partlyhuman/wqv-blink/firmware/wqv310/src/app.cpp

#include "app.h"

#include <algorithm>
#include <cstring>

#include "log.h"

namespace App {

const char* TAG = "App";

constexpr char RESPONSE_BDY0[] = "BDY0";
constexpr uint8_t RINF_EXTRA_DATA[]{0x00, 0x00, 0x10, 0xFF, 0xFF, 0x11, 0xFF, 0xFF};
constexpr uint8_t RCMD_EXTRA_DATA[]{0x00, 0x00, 0x20, 0x00, 0x01, 0x00, 0x01};
constexpr uint8_t RIMG_EXTRA_DATA[]{0x00, 0x00, 0x00, 0x01, 0x01, 0x01, 0x08, 0x00, 0x06, 0x00, 0x02, 0x07, 0x08,
                                    0x00, 0x06, 0x00, 0x06, 0x40, 0x04, 0xB0, 0x05, 0x00, 0x03, 0xC0, 0x04, 0x00,
                                    0x03, 0x00, 0x03, 0x20, 0x02, 0x58, 0x02, 0x80, 0x01, 0xE0, 0x01, 0x40, 0x00,
                                    0xF0, 0x03, 0xC4, 0x20, 0x04, 0x01, 0xC4, 0x20, 0x05, 0x00, 0x00, 0x18, 0x00};

std::span<const uint8_t> fill(std::span<const uint8_t> cmd, uint8_t session) {
    static std::vector<uint8_t> CMD_BUFFER(64);
    std::replace_copy(cmd.begin(), cmd.end(), CMD_BUFFER.begin(), SESH, session);
    return std::span(CMD_BUFFER).subspan(0, cmd.size());
}

// NOTE this expects the full frame, as a convenience it also acts on the session header
// even though that's not part of the application layer
std::vector<uint8_t> makeResponse(Frame::Frame frame) {
    const size_t CMD_SIZE = 44;
    if (frame.data.size() < CMD_SIZE) {
        LOGE(TAG, "Size too small to be app command packet");
        return {};
    }

    std::string cmd = getCmdName(frame);
    std::span<const uint8_t> extraData;
    int8_t shifts;
    if (cmd == "RINF") {
        extraData = RINF_EXTRA_DATA;
        shifts = -0x0C;
    } else if (cmd == "RCMD") {
        extraData = RCMD_EXTRA_DATA;
        shifts = -0x0D;
    } else if (cmd == "RIMG") {
        extraData = RIMG_EXTRA_DATA;
        shifts = 0x20;
    }
    std::vector<uint8_t> response(frame.data.begin(), frame.data.begin() + CMD_SIZE);
    response.reserve(response.size() + sizeof(uint32_t) + extraData.size());
    auto src = frame.data;

    // 1. First bytes: swap [session] 03 -> 03 [session]
    response[0] = src[1];
    response[1] = src[0];

    // 2. Last byte 0x2b: 02 -> 01
    response[0x2b] = 0x01;

    // 3. Byte 0xf: 00 -> 40
    response[0xf] = 0x40;

    // 4. Byte 0x18 & 0x20: swap
    response[0x18] = src[0x20];
    response[0x20] = src[0x18];

    // 5. Byte 0x29 unchanged

    // 6. Shifted fields
    response[0x9] = static_cast<uint8_t>(static_cast<int8_t>(src[0x9]) + shifts);
    response[0xd] = static_cast<uint8_t>(static_cast<int8_t>(src[0xd]) + shifts);
    response[0x13] = static_cast<uint8_t>(static_cast<int8_t>(src[0x13]) + shifts);

    // Append "BDY0" without \0
    response.insert(response.end(), std::begin(RESPONSE_BDY0), std::end(RESPONSE_BDY0) - 1);

    // Append 4-byte size of extended data
    uint32_t extraSize = static_cast<uint32_t>(extraData.size());
    response.push_back(static_cast<uint8_t>((extraSize >> 24) & 0xFF));
    response.push_back(static_cast<uint8_t>((extraSize >> 16) & 0xFF));
    response.push_back(static_cast<uint8_t>((extraSize >> 8) & 0xFF));
    response.push_back(static_cast<uint8_t>(extraSize & 0xFF));

    // Append extended data
    response.insert(response.end(), extraData.begin(), extraData.end());
    return response;
}

std::pair<std::string, std::vector<uint8_t>> makeFilRplResponse(Frame::Frame frame) {
    constexpr uint8_t RPL0_CMD[]{0,    0,    0x00, 0x00, 0x00, 0x20, 0x03, 0xFF, 0x00, 0x38, 0x10, 0xC1, 0x00, 0x34,
                                 0x58, 0x40, 0x00, 0x00, 0x00, 0x2E, 0x08, 0x00, 0x74, 0x03, 0x00, 0x00, 0x00, 0x00,
                                 0x08, 0x00, 0x74, 0x03, 0x10, 0x00, 0x00, 0x00, 0x00, 0x08, 0x00, 0x08, 0x00, 0,
                                 0x00, 0x01, 0x52, 0x50, 0x4C, 0x30, 0x00, 0x00, 0x00, 0x0E, 0x01, 0x00, 0x00, 0x00,
                                 0x00, 0x00, 0x00, 0x00, 0x00, 0x00, 0x00, 0x00, 0x00, 0x00};

    auto src = frame.data;
    std::vector<uint8_t> response(std::begin(RPL0_CMD), std::end(RPL0_CMD));
    response[0] = src[1];
    response[1] = src[0];
    response[0x29] = src[0x31];
    auto fileNameSpan = src.subspan(0x4C, 12);
    std::memcpy(response.data() + 0x36, fileNameSpan.data(), fileNameSpan.size());
    std::string fileName(reinterpret_cast<const char *>(fileNameSpan.data()), fileNameSpan.size());
    return {fileName, response};
}

std::string getCmdName(Frame::Frame frame) {
    return Frame::extractString(frame, frame.data.size() - 4, 4);
}

std::span<const uint8_t> getAppPayload(Frame::Frame frame) {
    if (frame.error || frame.data.size() < std::size(CLIENT_APP_PACKET)) {
        return {};
    }
    // Could reject if doesn't start with session header
    return frame.data.subspan(std::size(CLIENT_APP_PACKET));
}

}  // namespace App
