partlyhuman/wqv-blink/firmware/wqv310/src/meta.cpp

#include "meta.h"

#include <FFat.h>
#include <PSRamFS.h>

#include <cstring>
#include <ctime>

#include "log.h"
namespace Meta {

const static char *TAG = "Meta";

time_t timestampToTime(const Timestamp src) {
    tm t{};
    t.tm_year = (2000 + src.year2k) - 1900;
    t.tm_mon = src.month - 1;
    t.tm_mday = src.day;
    t.tm_hour = src.hour;
    t.tm_min = src.minute;
    t.tm_isdst = 0;
    time_t time = mktime(&t);
    return time;
}

void setSystemTime(const time_t time) {
    timeval epoch = {time, 0};
    settimeofday((const timeval *)&epoch, 0);
}

std::string trimTrailingSpaces(std::string src) {
    if (src.find_first_not_of(' ') == std::string::npos) return "";
    return src.substr(0, src.find_last_not_of(' ') + 1);
}

std::pair<std::string, Timestamp> getMetaFromJpegMarker(fs::File src) {
    try {
        // Let's make things easy on ourselves and assume the marker is in the first 512 bytes of the file
        char headerBuffer[512];
        if (!src) throw std::runtime_error("Couldn't find file");
        src.seek(0);
        size_t bytesRead = src.readBytes(headerBuffer, sizeof(headerBuffer));
        src.seek(0);

        std::span header(headerBuffer, headerBuffer + bytesRead);
        auto iter = header.begin();

        if (iter[0] != 0xff || iter[1] != 0xd8) throw std::runtime_error("Invalid SOI");
        iter += 2;

        // Make sure we at least have enough to read the marker
        while ((iter + 4) < header.end()) {
            if (iter[0] != 0xff) throw std::runtime_error("Expected 0xff in marker");
            uint8_t marker = iter[1];
            iter += 2;

            // len includes the bytes themselves, but we don't want to consume them
            uint16_t len = (iter[0] << 8) | iter[1];
            LOGV(TAG, "Encountered marker %02x of length %d", marker, len);
            if (marker != 0xe2) {
                iter += len;
                continue;
            }

            LOGD(TAG, "Found APP2 marker, extracting metadata");
            // consume the length too, we want to point to the data
            const char *payload = header.data() + (iter - header.begin()) + 2;
            size_t payloadLen = len - 2;

            if (payloadLen < sizeof(Timestamp)) throw std::runtime_error("APP2 marker not big enough for timestamp");

            size_t strLen = payloadLen - sizeof(Timestamp);
            Timestamp timestamp;
            std::memcpy(&timestamp, payload + strLen, sizeof(Timestamp));

            std::string title;
            bool isAscii = std::all_of(payload, payload + strLen, [](char b) { return b <= 0x7F; });
            if (isAscii) {
                title = trimTrailingSpaces(std::string(payload, strLen));
            }
            return std::pair(title, timestamp);
        }

        LOGE(TAG, "Couldn't find APP2 marker in JPEG, no metadata");

    } catch (std::exception &e) {
        LOGE(TAG, "%s", e.what());
    }
    return {};
}

bool copyRename(fs::File src, std::string destPath, size_t size) {
    auto startTime = millis();

    File dst = FFat.open(destPath.c_str(), "w");
    if (!dst) return false;

    // preallocate
    // size_t size = src.size(); // doesn't work on PSRAMFS, use passed size
    LOGD(TAG, "Preallocating copied file to %d bytes", size);
    dst.seek(size - 1);
    dst.write((uint8_t)0);
    dst.seek(0);

    // Buffered copy
    src.seek(0);
    static uint8_t buffer[4096];
    while (true) {
        size_t n = src.read(buffer, sizeof(buffer));
        if (n == 0) break;

        size_t written = dst.write(buffer, n);
        if (written != n) {
            LOGE(TAG, "Write error");
            dst.close();
            return false;
        }
    }

    dst.close();

    LOGD(TAG, "Copied file in %d ms", millis() - startTime);

    return true;
}

void postProcess(std::string fileName, size_t fileSize) {
    std::string dir = "/";

    // Reopen in read mode - I don't think rw mode worked, but actually TODO let me verify that
    fs::File src = PSRamFS.open((dir + fileName).c_str(), "r");
    if (!src) return;

    auto meta = getMetaFromJpegMarker(src);

    time_t time = timestampToTime(meta.second);
    setSystemTime(time);

    LOGI(TAG, "File %s has metadata time=%s title='%s'", fileName.c_str(), std::ctime(&time), meta.first.c_str());

    // TODO make a new filename using the timestamp
    std::string base = fileName.substr(0, fileName.size() - 4);

    if (meta.first.size() > 0) {
        auto file = FFat.open((dir + base + ".txt").c_str(), "w", true);
        file.println(meta.first.c_str());
        file.close();
    }

    // TODO because we now have to make a copy, let's in fact use PSRAMFS!!
    if (copyRename(src, dir + base + ".jpg", fileSize)) {
        src.close();
        LOGD(TAG, "Copied to flash, removing PSRAM copy");
        PSRamFS.remove((dir + fileName).c_str());
    }
}

}  // namespace Meta
