partlyhuman/wqv-blink/firmware/qv1ckenir/include/_1980v23P04_16.h

const uint8_t _1980v23P04_16Bitmaps[] PROGMEM = {
0x00, 0xDB, 0x6C, 0x30, 0xDB, 0x60, 0x66, 0x33, 0x3F, 0xCC, 0xCF, 0xF3, 0x31, 0x98, 0x10, 0xF3, 0x36, 0x07, 0x81, 0xB3, 0x3C, 0x20, 0xC6, 0xCE, 0x1C, 0x38, 0x70, 0xE6, 0xC6, 0x7C, 0x30, 0x0C, 0xC1, 0xFE, 0xCC, 0x33, 0x07, 0xB8, 0xD8, 0x76, 0x31, 0x8C, 0x61, 0xC0, 0xE1, 0x8C, 0x63, 0x1B, 0x80, 0x18, 0x6D, 0x9F, 0x9B, 0x61, 0x80, 0x30, 0x63, 0xF1, 0x83, 0x00, 0x66, 0xC0, 0xF0, 0xD8, 0x06, 0x0E, 0x1C, 0x38, 0x70, 0xE0, 0xC0, 0x79, 0x9B, 0x36, 0x6C, 0xD9, 0x9E, 0x00, 0x6E, 0x66, 0x66, 0x60, 0x79, 0x98, 0x30, 0xC3, 0x0C, 0x3F, 0x00, 0x79, 0x98, 0x31, 0xC0, 0xD9, 0x9E, 0x00, 0x1C, 0x3C, 0x6C, 0xCC, 0xFE, 0x0C, 0x0C, 0x7D, 0x83, 0xE0, 0x60, 0xD9, 0x9E, 0x00, 0x79, 0xE3, 0xE6, 0x6C, 0xD9, 0x9E, 0x00, 0xFC, 0x18, 0x61, 0x86, 0x0C, 0x18, 0x00, 0x79, 0x9B, 0x33, 0xCC, 0xD9, 0x9E, 0x00, 0x79, 0x9B, 0x36, 0x63, 0xC1, 0x9E, 0x00, 0xD8, 0x6C, 0x66, 0x06, 0x6C, 0x1C, 0x71, 0xC7, 0x07, 0x07, 0x07, 0x00, 0xF0, 0x3C, 0xE0, 0xE0, 0xE0, 0xE3, 0x8E, 0x38, 0x00, 0xF8, 0x18, 0x33, 0xE6, 0x00, 0x18, 0x00, 0x3F, 0x08, 0x12, 0x7D, 0x59, 0xAB, 0x35, 0x66, 0xA7, 0xE2, 0x00, 0x3F, 0xC0, 0x79, 0x9B, 0x37, 0xEC, 0xD9, 0xB3, 0x00, 0xF9, 0x9B, 0x37, 0xCC, 0xD9, 0xBE, 0x00, 0x79, 0x9B, 0x06, 0x0C, 0x19, 0x9E, 0x00, 0xF9, 0x9B, 0x36, 0x6C, 0xD9, 0xBE, 0x00, 0xFB, 0x0C, 0x3E, 0xC3, 0x0F, 0x80, 0xFB, 0x0C, 0x3E, 0xC3, 0x0C, 0x00, 0x7D, 0x83, 0x06, 0x6C, 0xD9, 0x9F, 0x00, 0xCD, 0x9B, 0x37, 0xEC, 0xD9, 0xB3, 0x00, 0xDB, 0x6D, 0xB0, 0x18, 0x61, 0x86, 0x18, 0x6F, 0x00, 0xCD, 0x9B, 0x37, 0xCC, 0xD9, 0xB3, 0x00, 0xC3, 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
	{	186,	7,	7,	7,	0,	-6},
	{	193,	7,	7,	7,	0,	-6},
	{	200,	7,	7,	7,	0,	-6},
	{	207,	6,	7,	6,	0,	-6},
	{	213,	6,	7,	6,	0,	-6},
	{	219,	7,	7,	7,	0,	-6},
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
};
const GFXfont _1980v23P04_16 PROGMEM = {
    (uint8_t *)_1980v23P04_16Bitmaps,
    (GFXglyph *)_1980v23P04_16Glyphs,
    0x20, 0x7E, 17};
